ArminRehberger/LED-Matrix-DCF77-and-Teensy-4.0/KiCad/LEDMatrixDCF77.kicad_pcb

## KiCad design KiCAD/stm8-gamepad/nucleo-8s207k8.kicad_sch

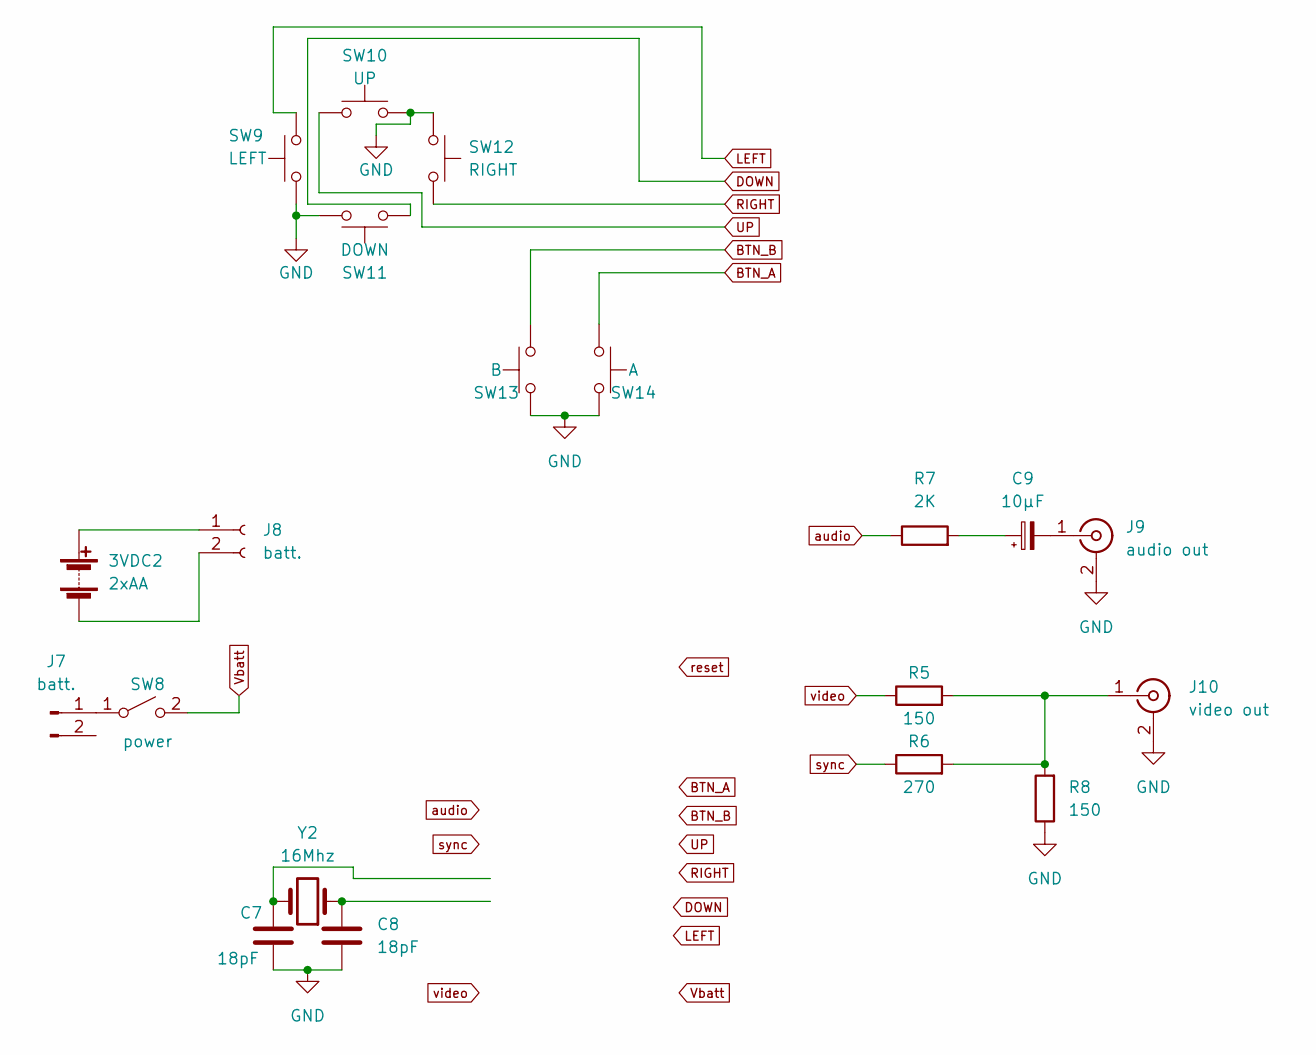
[picture p4: schematic nucleo-8s207k8.kicad_sch]

Parts:
3VDC2: 2xAA
C7, C8: 18pF
C9: 10µF
J7, J8: batt.
J9: audio out
J10: video out
R5, R8: 150
R6: 270
R7: 2K
SW8: power
SW9: LEFT
SW10: UP
SW11: DOWN
SW12: RIGHT
SW13: B
SW14: A
Y2: 16Mhz

Connections:
BTN_A: SW14.1 (A), SW14.2 (A)
BTN_B: SW13.3 (B), SW13.4 (B)
DOWN: SW11.1 (A), SW11.2 (A)
GND: C7.2, C8.2, J9.2 (Ext), J10.2 (Ext), R8.1, SW9.1 (A), SW9.2 (A), SW10.3 (B), SW10.4 (B), SW11.3 (B), SW11.4 (B), SW12.1 (A), SW12.2 (A), SW13.1 (A), SW13.2 (A), SW14.3 (B), SW14.4 (B)
LEFT: SW9.3 (B), SW9.4 (B)
unnamed: 3VDC2.1 (+), J8.1
unnamed: 3VDC2.2 (-), J8.2
unnamed: C7.1, Y2.2
unnamed: C8.1, Y2.1
unnamed: C9.1, R7.2
unnamed: C9.2, J9.1 (In)
unnamed: J7.1, SW8.1 (A)
unnamed: J10.1 (In), R5.2, R6.2, R8.2
RIGHT: SW12.3 (B), SW12.4 (B)
UP: SW10.1 (A), SW10.2 (A)
Vbatt: SW8.2 (B)
audio: R7.1
sync: R6.1
video: R5.1
